asrob-uc3m/robotDevastation-robots/QR/1.png

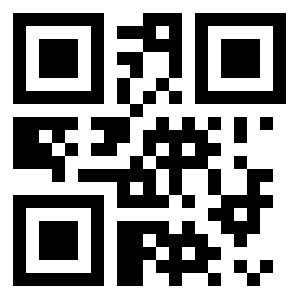
QR/1.png
