asrob-uc3m/robotDevastation-robots/QR/2.png

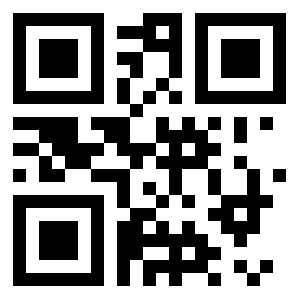
QR/2.png
