asrob-uc3m/robotDevastation-robots/QR/3.png

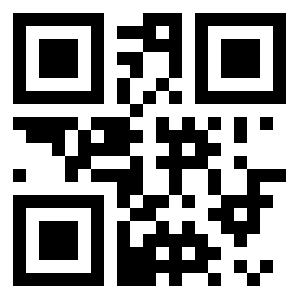
QR/3.png
