asrob-uc3m/robotDevastation-robots/QR/4.png

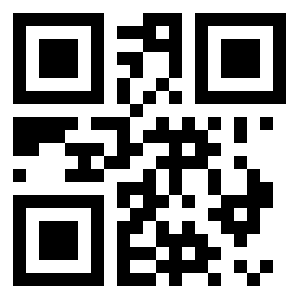
QR/4.png
