asrob-uc3m/robotDevastation-robots/QR/5.png

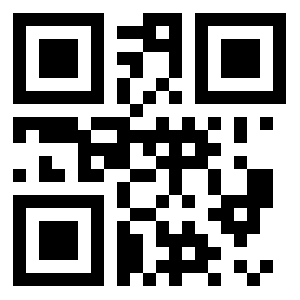
QR/5.png
