asrob-uc3m/robotDevastation-robots/ecro/necro/supportA.fcstd

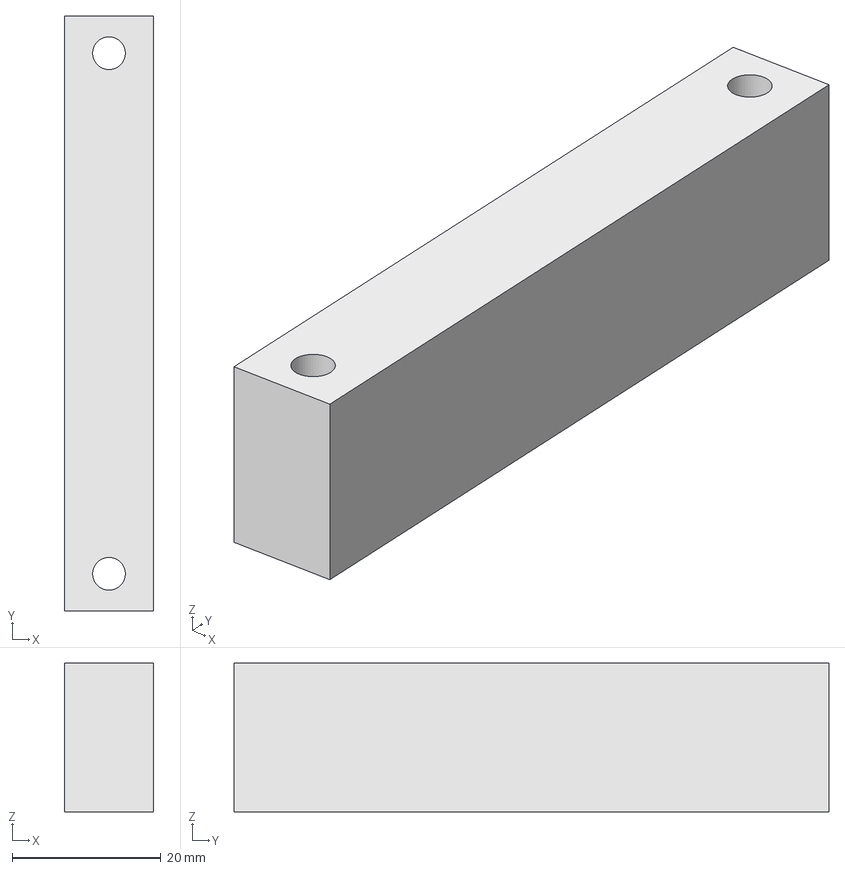
[picture p20: CAD file, 2017-01-13]
ecro/necro/supportA.fcstd
12.0 x 80.0 x 20.0 mm
