asrob-uc3m/robotDevastation-robots/rd2/mechanics/rd2BaseV1_0.STL

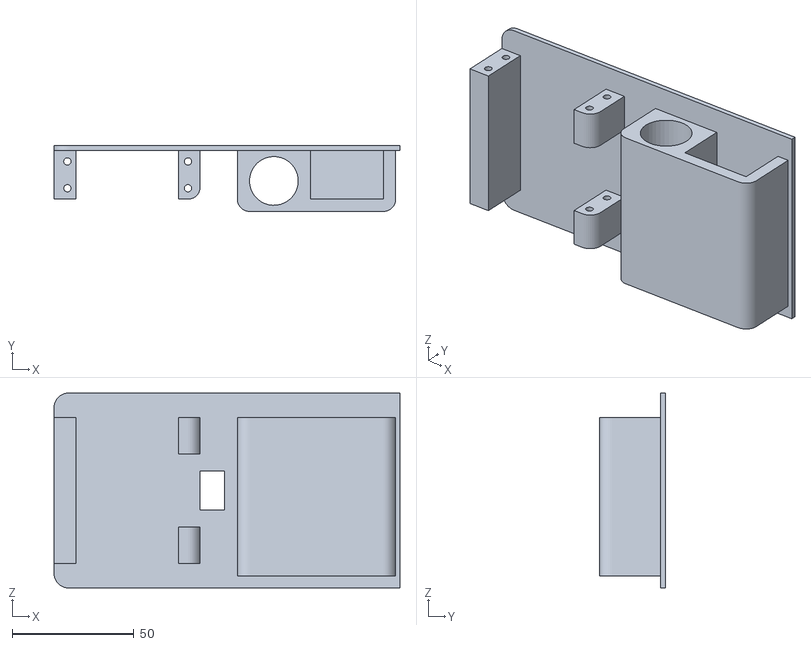
[picture p21: CAD file, 2015-04-27]
rd2/mechanics/rd2BaseV1_0.STL
142.0 x 27.0 x 80.0
